fonske/clack-reader-v4/readme/dp_sw_functionality.jpg

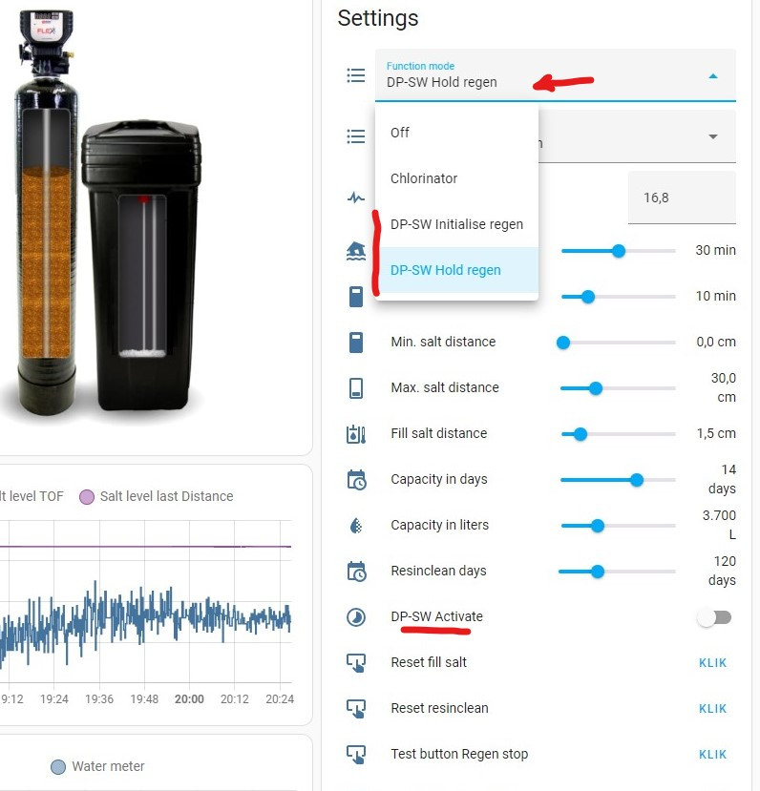
readme/dp_sw_functionality.jpg
