fonske/clack-reader-v4/readme/pcb_back.jpg

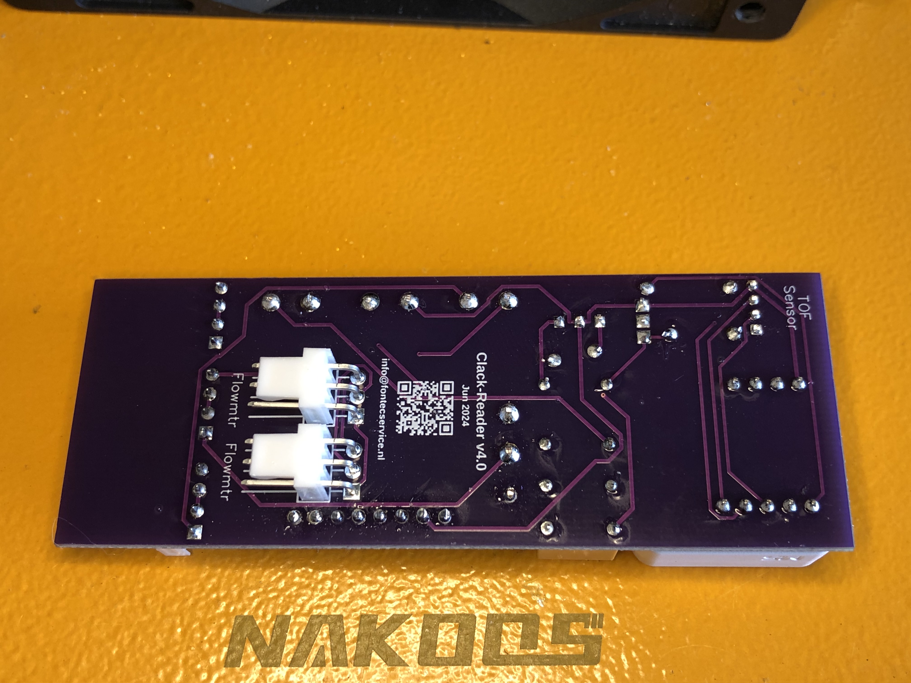
readme/pcb_back.jpg
