fonske/clack-reader-v4/www/images/softener0.png

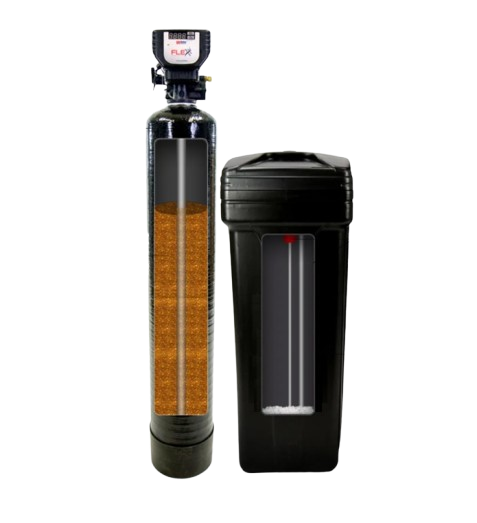
www/images/softener0.png
