fonske/clack-reader-v4/www/images/softener80.png

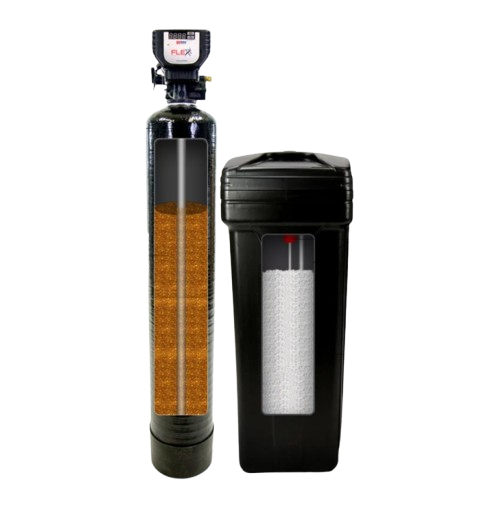
www/images/softener80.png
