fonske/clack-reader-v4/readme/last_changes_august_2024.jpg

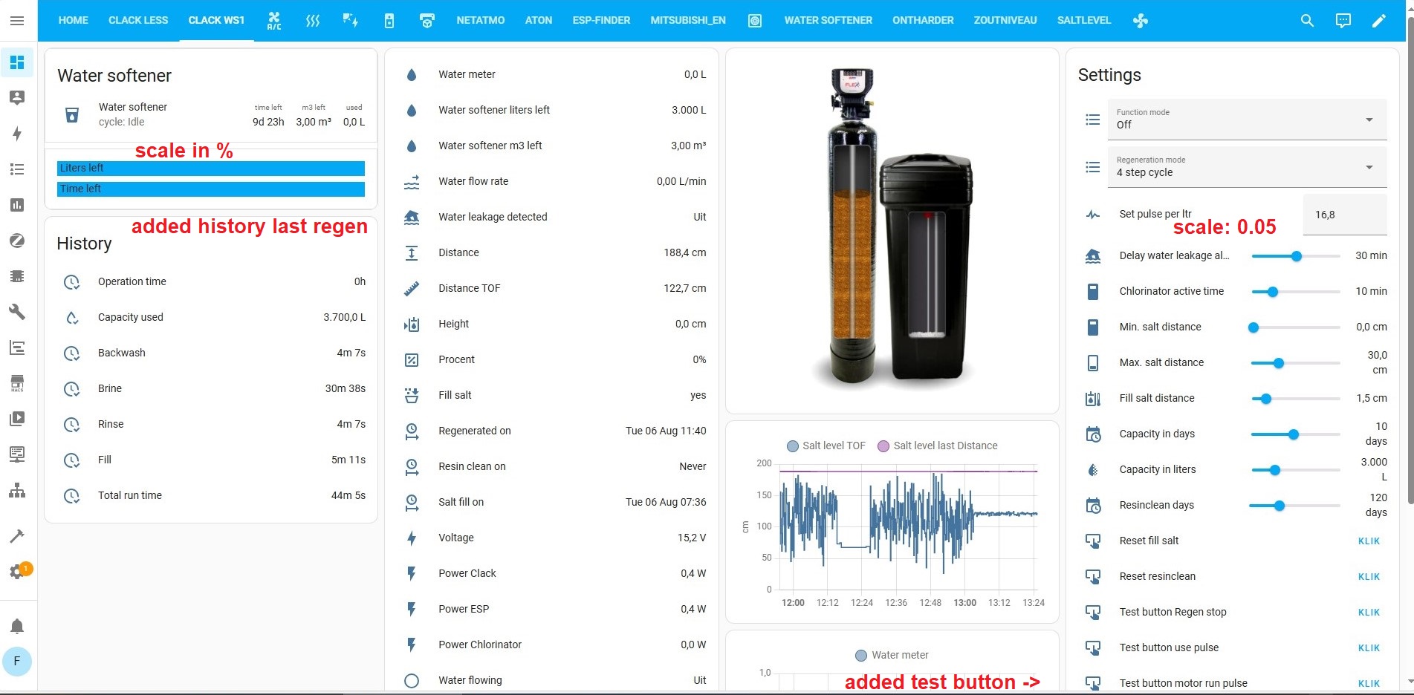
readme/last_changes_august_2024.jpg
